RepRapLtd/EchoPi/Pictures/Raw/IMG_2708.JPG

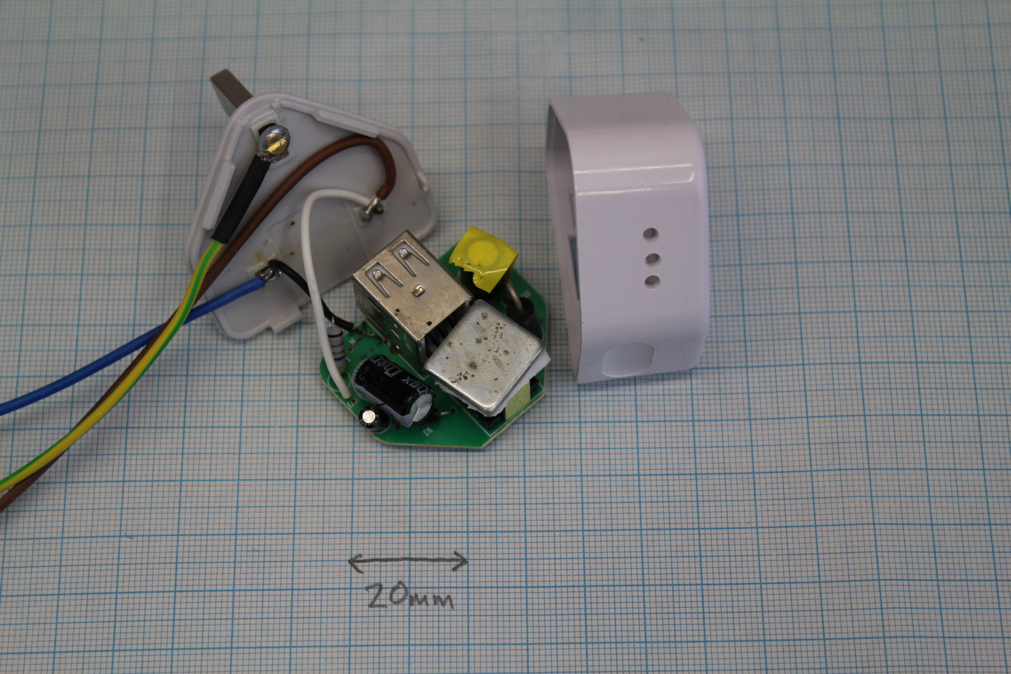
Pictures/Raw/IMG_2708.JPG
