RepRapLtd/EchoPi/Pictures/Raw/IMG_2709.JPG

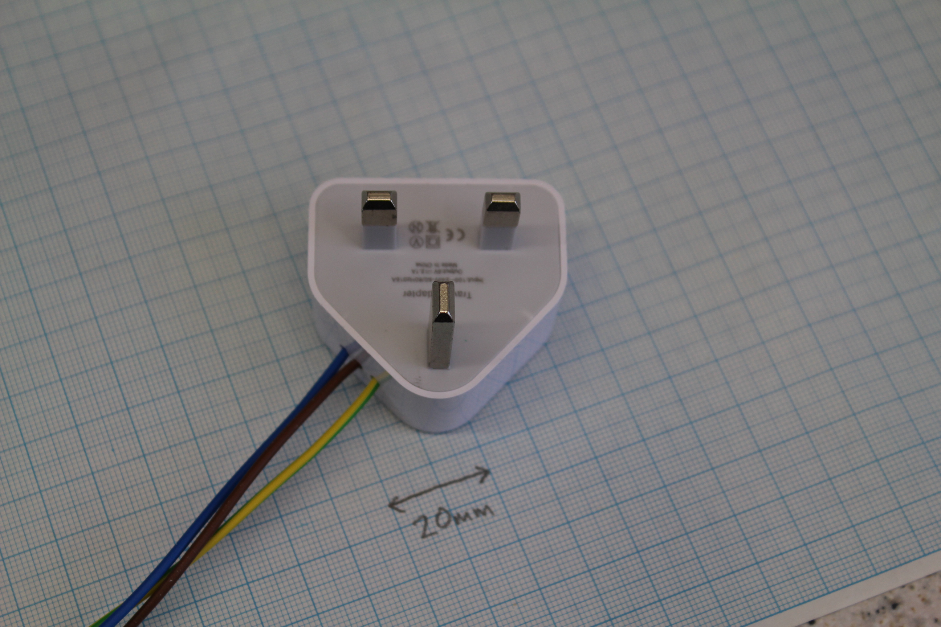
Pictures/Raw/IMG_2709.JPG
