RepRapLtd/EchoPi/Pictures/Raw/IMG_2710.JPG

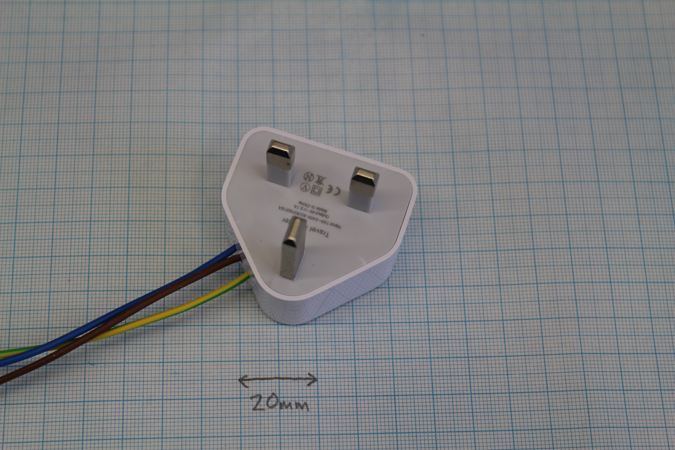
Pictures/Raw/IMG_2710.JPG
