RepRapLtd/EchoPi/Pictures/Raw/IMG_2711.JPG

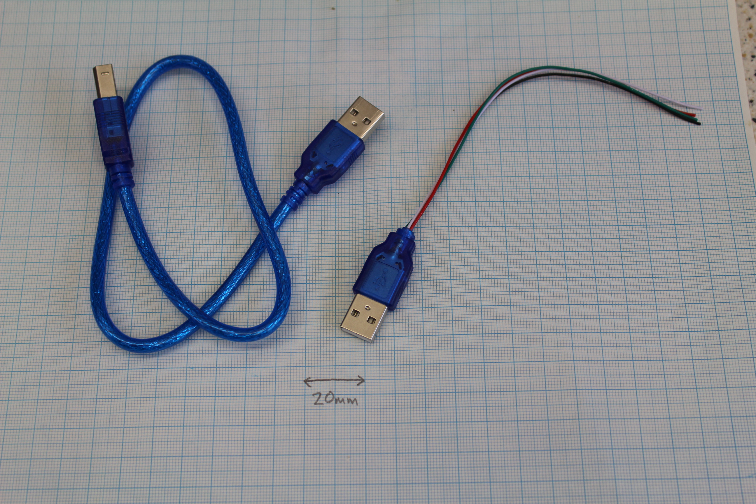
Pictures/Raw/IMG_2711.JPG
