RepRapLtd/EchoPi/Pictures/Raw/IMG_2712.JPG

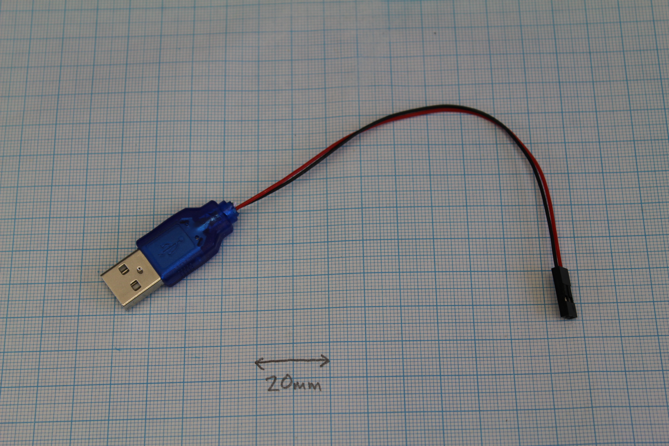
Pictures/Raw/IMG_2712.JPG
