RepRapLtd/EchoPi/Pictures/Raw/IMG_2713.JPG

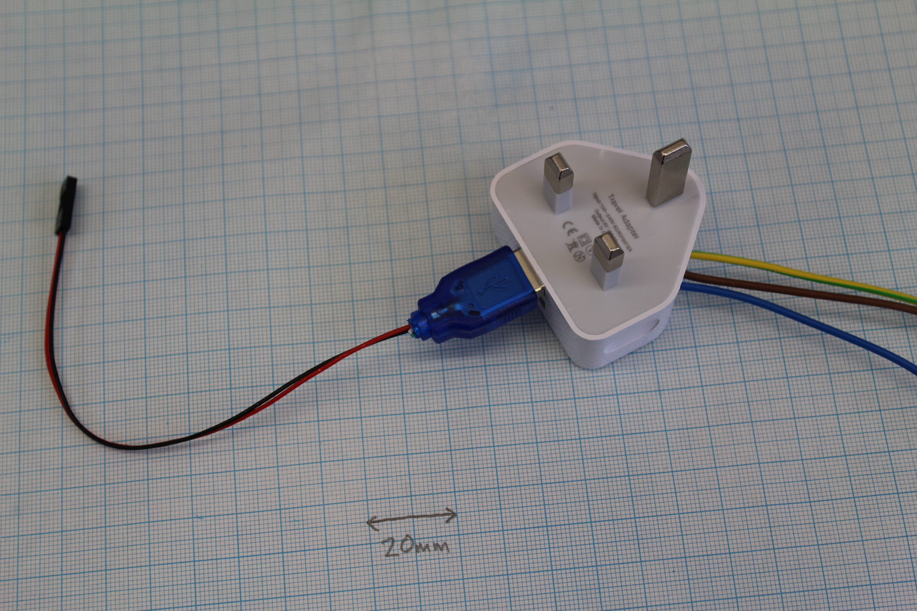
Pictures/Raw/IMG_2713.JPG
